p4nd4m01um/team17/ScreenShot/main.png

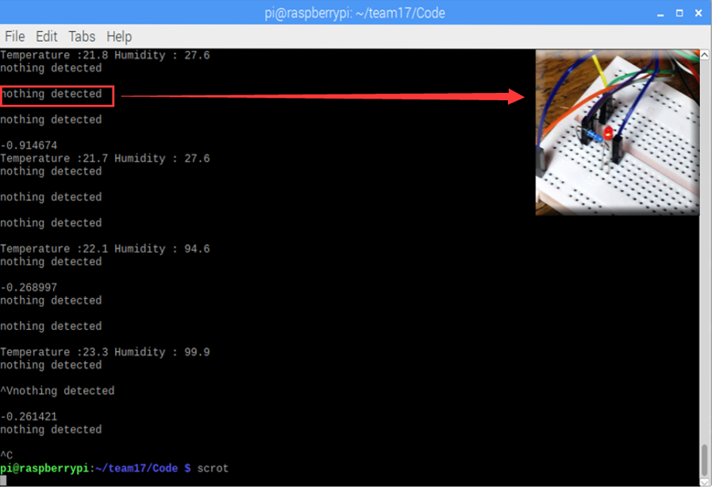
ScreenShot/main.png
