p4nd4m01um/team17/ScreenShot/pcbBottomLayer.PNG

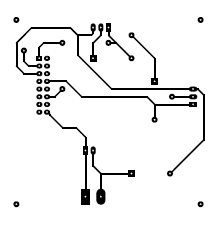
ScreenShot/pcbBottomLayer.PNG
