p4nd4m01um/team17/ScreenShot/pcbMotorBottomLayer.PNG

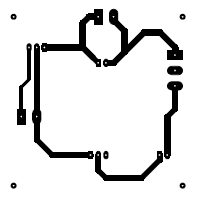
ScreenShot/pcbMotorBottomLayer.PNG
