p4nd4m01um/team17/ScreenShot/pcbMotorLayout.PNG

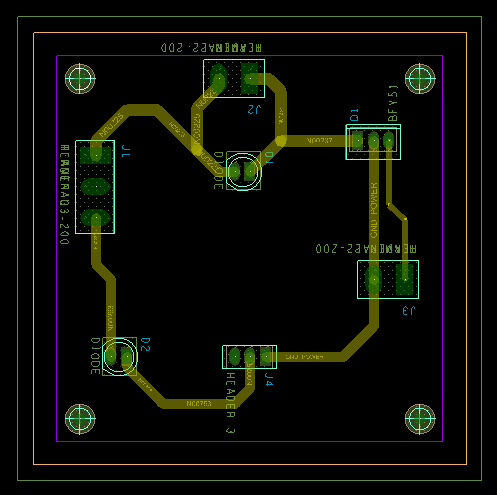
ScreenShot/pcbMotorLayout.PNG
