p4nd4m01um/team17/ScreenShot/pcbMotorToplayer.PNG

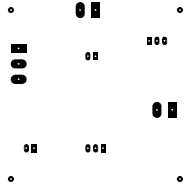
ScreenShot/pcbMotorToplayer.PNG
