p4nd4m01um/team17/ScreenShot/powerOff.png

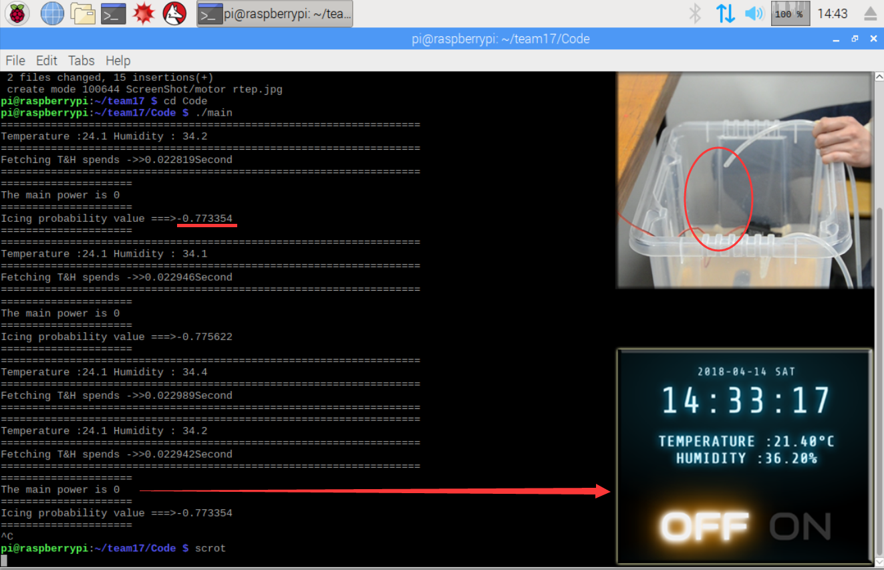
ScreenShot/powerOff.png
