p4nd4m01um/team17/ScreenShot/web.png

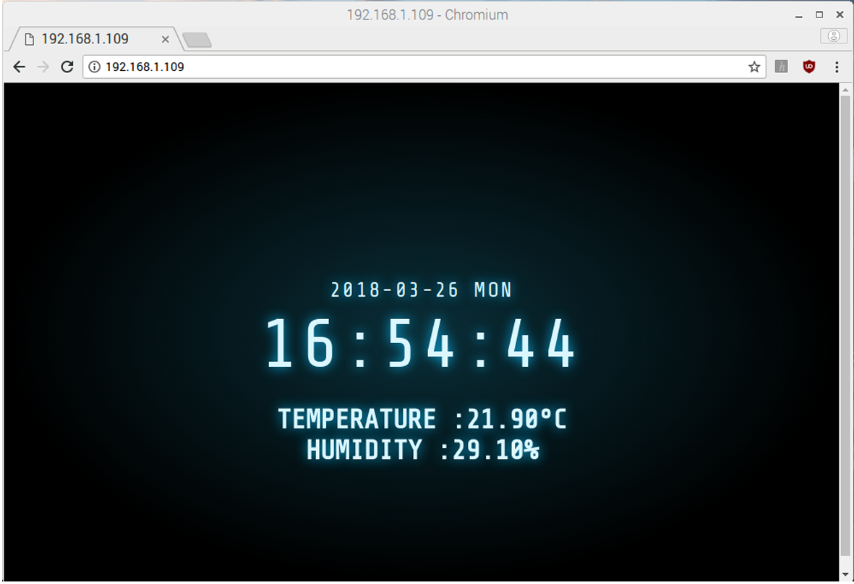
ScreenShot/web.png
